ThatguyCplus/truck-switch-reverse-eng/photos/03-component-side-alt.jpg

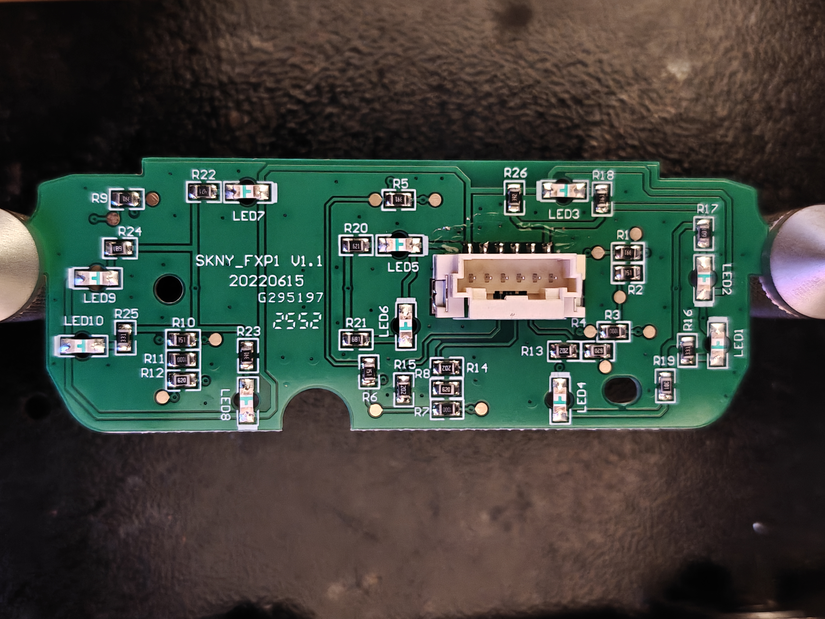
photos/03-component-side-alt.jpg
