ThatguyCplus/truck-switch-reverse-eng/photos/04-component-side-alt.jpg

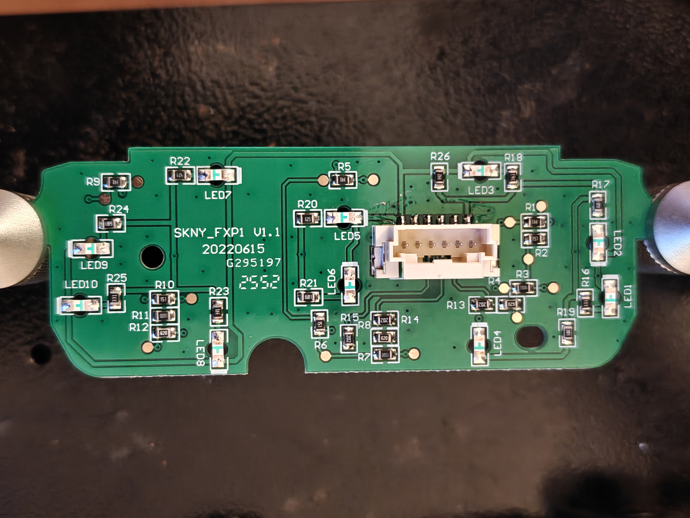
photos/04-component-side-alt.jpg
