ThatguyCplus/truck-switch-reverse-eng/hardware/UIbuttons.kicad_sch

## KiCad design hardware/UIbuttons.kicad_sch (2026-08-11)

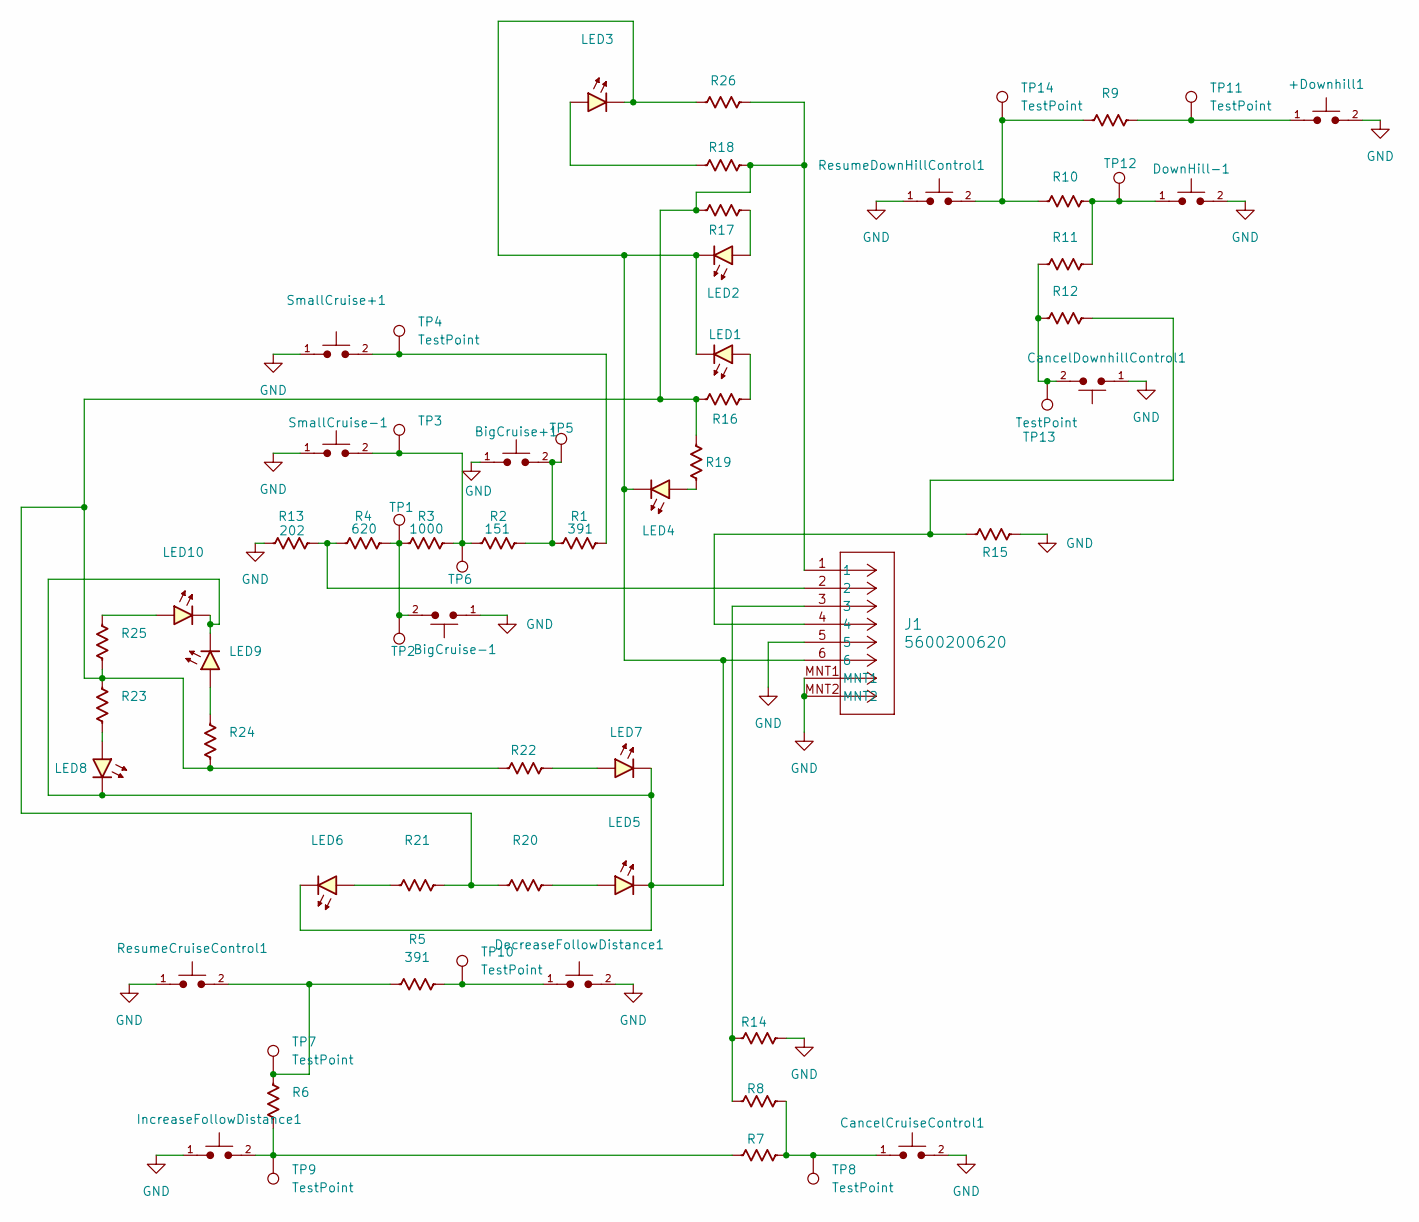
[picture p14: schematic UIbuttons.kicad_sch]

Parts:
+Downhill1: Push_Button; Push_SMD_6x3.5mm
BigCruise+1: Push_Button; Push_SMD_6x3.5mm
BigCruise-1: Push_Button; Push_SMD_6x3.5mm
CancelCruiseControl1: Push_Button; Push_SMD_6x3.5mm
CancelDownhillControl1: Push_Button; Push_SMD_6x3.5mm
DecreaseFollowDistance1: Push_Button; Push_SMD_6x3.5mm
DownHill-1: Push_Button; Push_SMD_6x3.5mm
IncreaseFollowDistance1: Push_Button; Push_SMD_6x3.5mm
J1: 5600200620; CONN_SD-560020-001_06_MOL
LED1, LED2, LED3, LED4, LED5, LED6, LED7, LED8, LED9, LED10: LED_1206_White; LED_1206_3216Metric
R1, R5, R9, R23: 391; R_0805_2012Metric
R2, R6, R10: 151; R_0805_2012Metric
R3, R7, R11: 1000; R_0805_2012Metric
R4, R8, R12: 620; R_0805_2012Metric
R13, R14, R15: 202; R_0805_2012Metric
R16, R25: 331; R_0805_2012Metric
R17, R21, R24: 681; R_0805_2012Metric
R18: 361; R_0805_2012Metric
R19: 301; R_0805_2012Metric
R20: 621; R_0805_2012Metric
R22: 471; R_0805_2012Metric
R26: 392; R_0805_2012Metric
ResumeCruiseControl1: Push_Button; Push_SMD_6x3.5mm
ResumeDownHillControl1: Push_Button; Push_SMD_6x3.5mm
SmallCruise+1: Push_Button; Push_SMD_6x3.5mm
SmallCruise-1: Push_Button; Push_SMD_6x3.5mm
TP1, TP2, TP3, TP4, TP5, TP6, TP7, TP8, TP9, TP10, TP11, TP12, TP13, TP14: TestPoint; TestPoint_Pad_D1.5mm

Connections:
GND: +Downhill1.2, BigCruise+1.1, BigCruise-1.1, CancelCruiseControl1.2, CancelDownhillControl1.1, DecreaseFollowDistance1.2, DownHill-1.2, IncreaseFollowDistance1.1, J1.5, J1.MNT1, J1.MNT2, R13.1, R14.2, R15.2, ResumeCruiseControl1.1, ResumeDownHillControl1.1, SmallCruise+1.1, SmallCruise-1.1
unnamed: +Downhill1.1, R9.2, TP11.1
unnamed: BigCruise+1.2, R1.2, R2.2, TP5.1
unnamed: BigCruise-1.2, R3.1, R4.2, TP1.1, TP2.1
unnamed: CancelCruiseControl1.1, R7.2, R8.2, TP8.1
unnamed: CancelDownhillControl1.2, R11.1, R12.1, TP13.1
unnamed: DecreaseFollowDistance1.1, R5.2, TP10.1
unnamed: DownHill-1.1, R10.2, R11.2, TP12.1
unnamed: IncreaseFollowDistance1.2, R6.1, R7.1, TP9.1
unnamed: J1.1, R16.2, R17.2, R18.1, R19.2, R20.1, R21.1, R22.1, R23.2, R24.2, R25.2, R26.1
unnamed: J1.2, R4.1, R13.2
unnamed: J1.3, R8.1, R14.1
unnamed: J1.4, R12.2, R15.1
unnamed: J1.6, LED1.1 (K), LED2.1 (K), LED3.1 (K), LED4.1 (K), LED5.1 (K), LED6.1 (K), LED7.1 (K), LED8.1 (K), LED9.1 (K), LED10.1 (K), R26.2
unnamed: LED1.2 (A), R16.1
unnamed: LED2.2 (A), R17.1
unnamed: LED3.2 (A), R18.2
unnamed: LED4.2 (A), R19.1
unnamed: LED5.2 (A), R20.2
unnamed: LED6.2 (A), R21.2
unnamed: LED7.2 (A), R22.2
unnamed: LED8.2 (A), R23.1
unnamed: LED9.2 (A), R24.1
unnamed: LED10.2 (A), R25.1
unnamed: R1.1, SmallCruise+1.2, TP4.1
unnamed: R2.1, R3.2, SmallCruise-1.2, TP3.1, TP6.1
unnamed: R5.1, R6.2, ResumeCruiseControl1.2, TP7.1
unnamed: R9.1, R10.1, ResumeDownHillControl1.2, TP14.1
